Nabinho/Everything-Controller-V2.0/Hardware/Everything_Controller_V2.0/3d/10K C3031 potentiometer.STEP

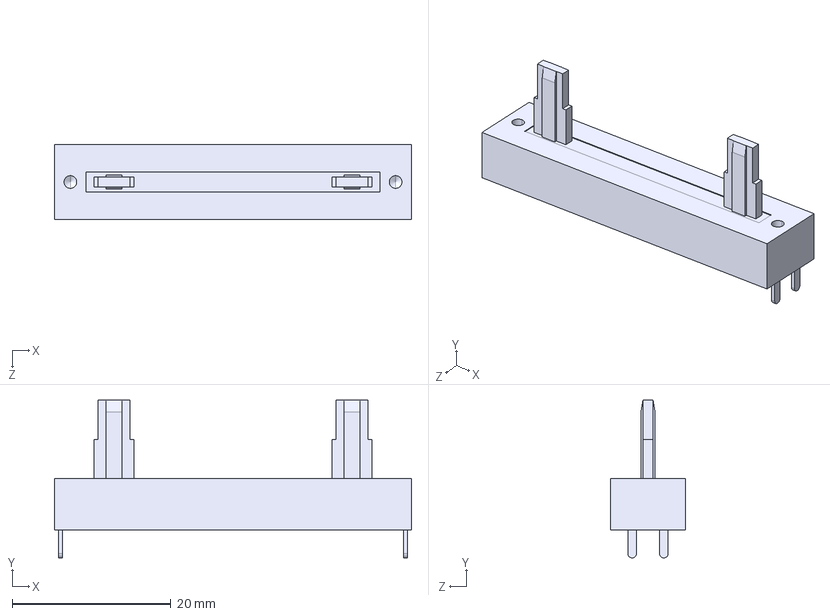
[picture p21: CAD file, 2024-03-24]
Hardware/Everything_Controller_V2.0/3d/10K C3031 potentiometer.STEP
45.0 x 19.9 x 9.50 mm
