Nabinho/Everything-Controller-V2.0/Hardware/Everything_Controller_V2.0/3d/SparkFun Deluxe Thumbstick with Breakout Board and Knob.step

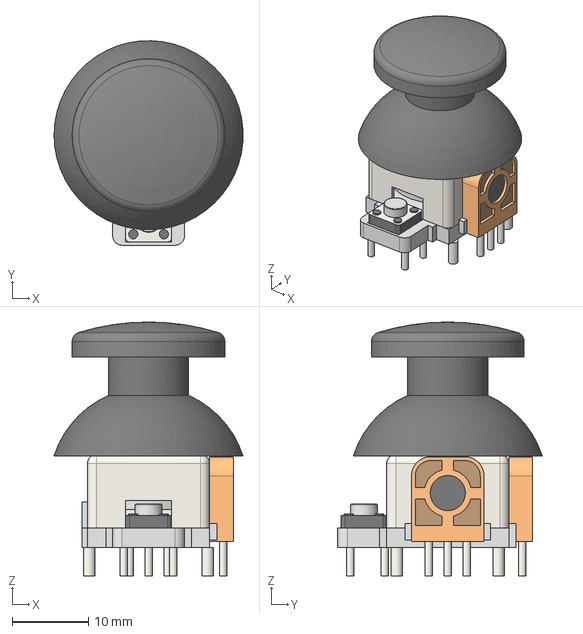
[picture p22: CAD file, 2024-03-24]
Hardware/Everything_Controller_V2.0/3d/SparkFun Deluxe Thumbstick with Breakout Board and Knob.step
24.7 x 26.8 x 33.2 mm
